PR77/CH554_USBQuadMouse/Software/include/serial.h

/********************************** (C) COPYRIGHT *******************************
* File Name     : SERIAL.H
* Author        : Paul Raspa (PR77)
* License       : MIT
* Version       : V1.0
* Date          : 2025/02/05
* Description   : 8051 UART Common
*******************************************************************************/

#ifndef __CH554_SERIAL_H__
#define __CH554_SERIAL_H__

#include <stdint.h>
#include "ch554.h"
#include "serial_0.h"
#include "serial_1.h"

void serial_printString(char* string);
void serial_printHexByte(uint8_t value);
void serial_printHexWord(uint16_t value);

#endif // __CH554_SERIAL_H__
