PR77/CH554_USBQuadMouse/Software/src/serial.c

/********************************** (C) COPYRIGHT *******************************
* File Name     : SERIAL.C
* Author        : Paul Raspa (PR77)
* License       : MIT
* Version       : V1.0
* Date          : 2025/02/06
* Description   : 8051 UART Common
*******************************************************************************/

#include <stdint.h>
#include <compiler.h>
#include "ch554.h"
#include "serial_0.h"
#include "serial_1.h"
#include "serial_cfg.h"

// HEX encoding table
static const uint8_t hexTable[] = {
    '0', '1', '2', '3',
    '4', '5', '6', '7',
    '8', '9', 'A', 'B',
    'C', 'D', 'E', 'F'
};

void serial_printString(char* string) {

    if (!string) {
        return;
    }
    
    while (*string) {
        // Repeat until string terminator reached printing each character
        // on the console.
        CONSOLE_PORT_PUTCHR(*string++);
    }
}

void serial_printHexByte(uint8_t value) {
    CONSOLE_PORT_PUTCHR(hexTable[(value >> 4)]);
    CONSOLE_PORT_PUTCHR(hexTable[value & 0x0F]);
}

void serial_printHexWord(uint16_t value) {
    serial_printHexByte(value >> 8);
    serial_printHexByte(value & 0xFF);
}
